gabrielsouza95/CarManGUI/Testes Arduino/teste_temp/teste_temp.ino

#include <Adafruit_MLX90614.h>
#include <Wire.h>
#include <MPU6050.h>

const int MPU = 0x68;
int16_t AcX = 0, AcY = 0, AcZ = 0, GyX = 0, GyY = 0, GyZ = 0; //MPU 1

Adafruit_MLX90614 mlx = Adafruit_MLX90614();

void setup() {
  // put your setup code here, to run once:
  Serial.begin(9600);
  Serial.println("Adafruit MLX90614 test");  
  mlx.begin(); 

  //POWER MANAGEMENT RELATED 
  Wire.beginTransmission(MPU); //escrevendo no endereço do MPU
  Wire.write(0x6B);            //acessando registrador responsável
  Wire.write(0b00000000);      //seta o sleep do MPU-6050 em 0  
  Wire.endTransmission();      //termina a configuração //talvez colocar false para não dar problema com o MLX

  //GYRO CONFIG RELATED
  Wire.beginTransmission(MPU);
  Wire.write(0x1B);
  Wire.write(0b00000000);
  Wire.endTransmission();//talvez colocar false para não dar problema com o MLX

  //ACCELEROMETER CONFIG RELATED
  Wire.beginTransmission(MPU);
  Wire.write(0x1C);
  Wire.write(0b00000000);
  Wire.endTransmission();//talvez colocar false para não dar problema com o MLX
}

void loop() {
  // put your main code here, to run repeatedly:
  Serial.print("Ambient = "); Serial.print(mlx.readAmbientTempC()); 
  Serial.print("*C\tObject = "); Serial.print(mlx.readObjectTempC()); Serial.println("*C");
  Serial.print("Ambient = "); Serial.print(mlx.readAmbientTempF()); 
  Serial.print("*F\tObject = "); Serial.print(mlx.readObjectTempF()); Serial.println("*F");
  Serial.println();
  //Gyro
  Wire.beginTransmission(MPU);
  Wire.write(0x43);
  Wire.endTransmission(); //talvez colocar false para não dar problema com o MLX
  Wire.requestFrom(MPU, 6);
  while(Wire.available() < 6);
  GyX = Wire.read()<<8|Wire.read(); //0x43 (GYRO_XOUT_H) & 0x44 (GYRO_XOUT_L)  
  GyY = Wire.read()<<8|Wire.read(); //0x45 (GYRO_YOUT_H) & 0x46 (GYRO_YOUT_L)  
  GyZ = Wire.read()<<8|Wire.read(); //0x47 (GYRO_ZOUT_H) & 0x48 (GYRO_ZOUT_L)     
  //Accel
  Wire.beginTransmission(MPU);
  Wire.write(0x3B);
  Wire.endTransmission(); //talvez colocar false para não dar problema com o MLX
  Wire.requestFrom(MPU, 6);
  while(Wire.available() < 6);
  AcX = Wire.read()<<8|Wire.read(); //0x43 (GYRO_XOUT_H) & 0x44 (GYRO_XOUT_L)  
  AcY = Wire.read()<<8|Wire.read(); //0x45 (GYRO_YOUT_H) & 0x46 (GYRO_YOUT_L)  
  AcZ = Wire.read()<<8|Wire.read(); //0x47 (GYRO_ZOUT_H) & 0x48 (GYRO_ZOUT_L)    
  Serial.print(GyX);//1
  Serial.print(":");
  Serial.print(GyY);//2
  Serial.print(":");
  Serial.print(GyZ);//3
  Serial.print(":");
  Serial.print(AcX);//4
  Serial.print(":");
  Serial.print(AcY);//5
  Serial.print(":");
  Serial.print(AcZ);//6
  Serial.print(":");
  delay(200);
}
